abel09011/R.I.K.-Robot-Interactive-K-9/Solid Work Parts/Head 5.SLDPRT

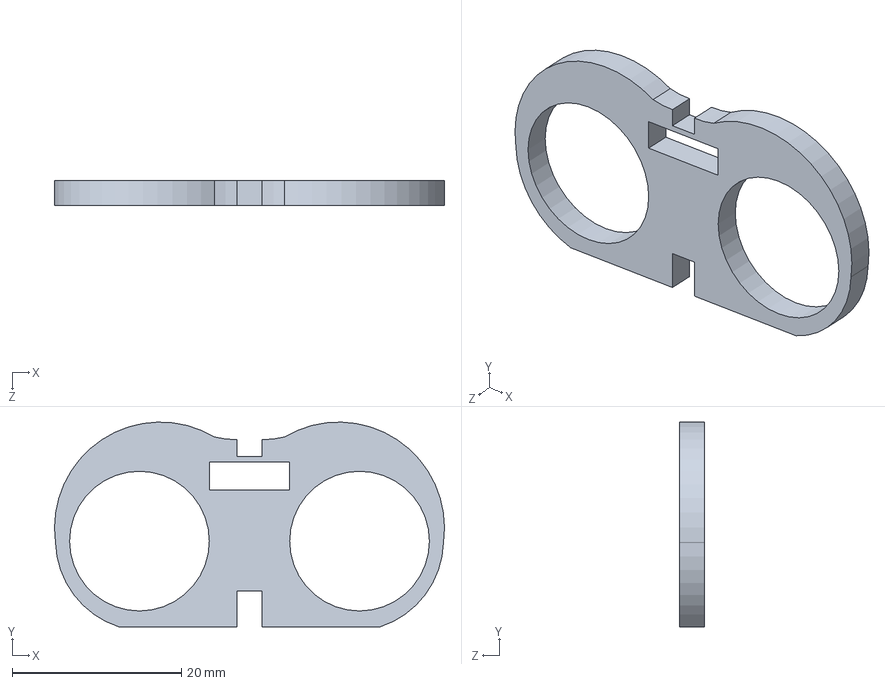
[picture p30: CAD file, 2019-06-04]
Solid Work Parts/Head 5.SLDPRT
46.1 x 24.2 x 3.00 mm
